dennowiggle/ESP32_Interface/sw/Z80-Programmer/include/version.h

#ifndef BUILD_NUMBER
  #define BUILD_NUMBER "2462"
#endif
#ifndef VERSION
  #define VERSION "v0.1.2462 - 2024-12-19 08:41:16.806757"
#endif
#ifndef VERSION_SHORT
  #define VERSION_SHORT "v0.1.2462"
#endif
